tobycm/skibidi-phone-usb-hub/pcb/skibidi-phone-usb-hub.kicad_sch

## KiCad design pcb/skibidi-phone-usb-hub.kicad_sch (2026-04-20)

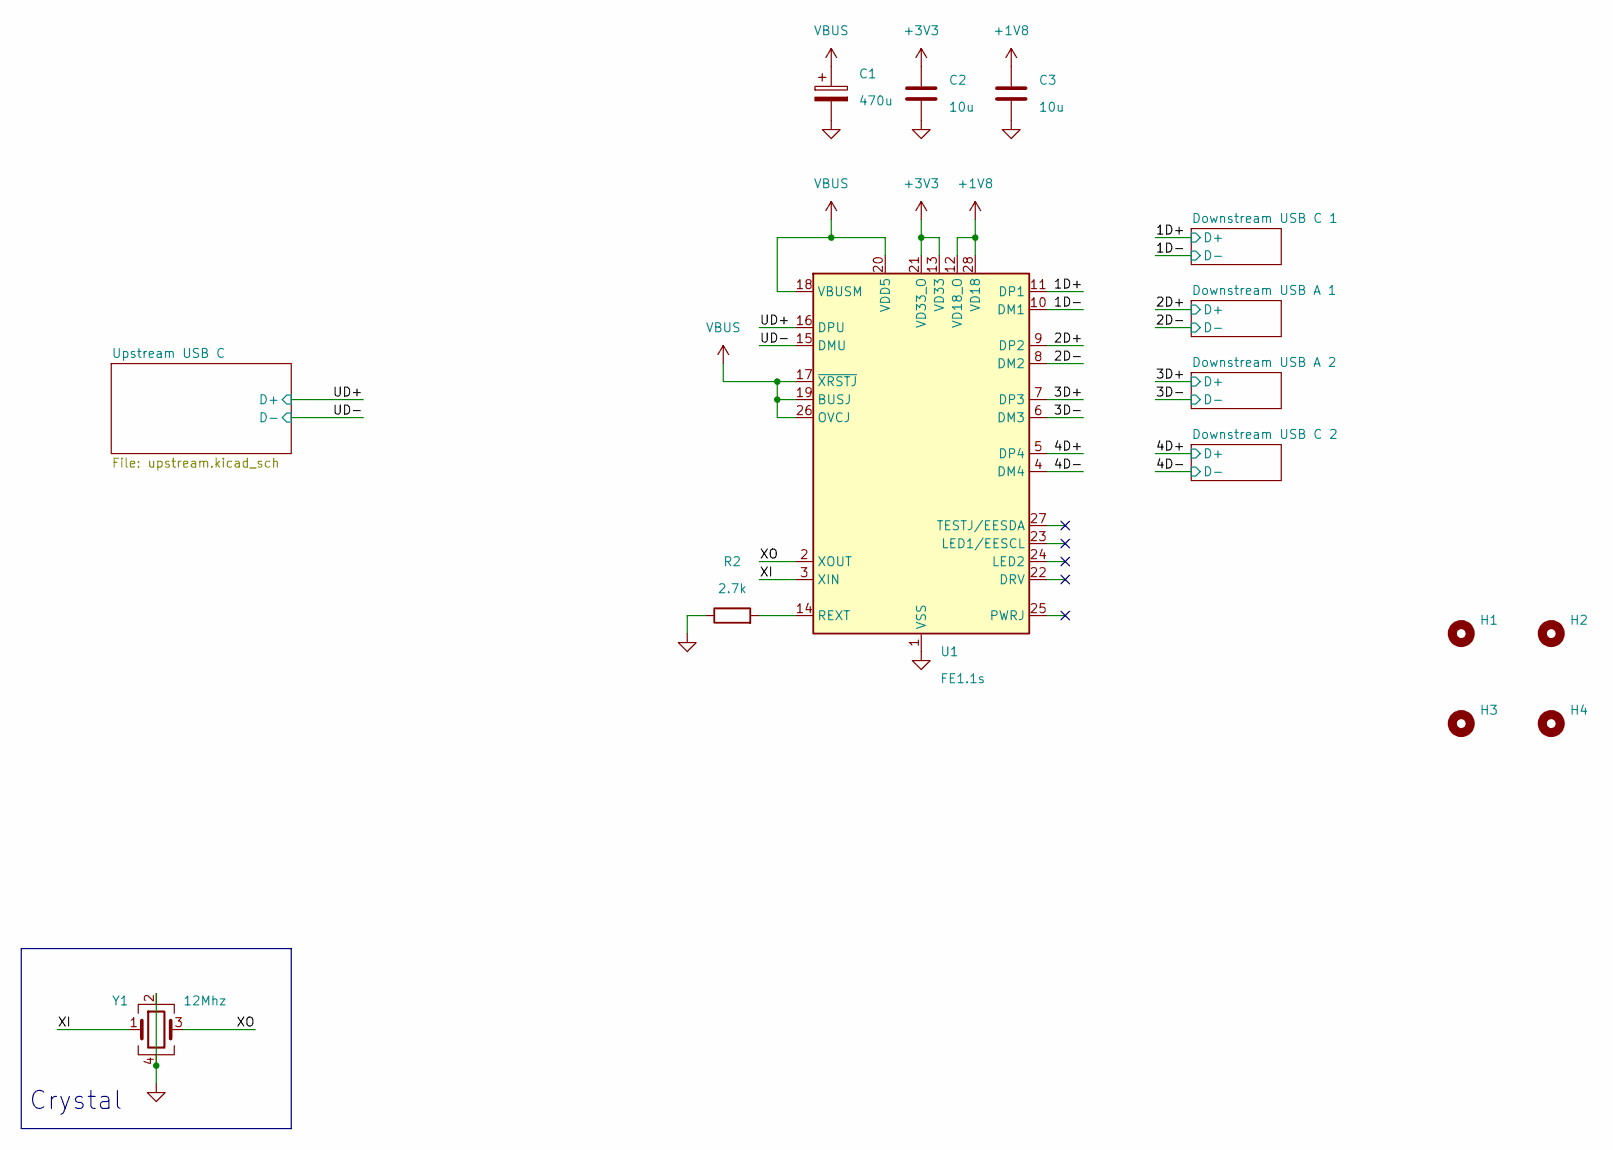
[picture p19: schematic skibidi-phone-usb-hub.kicad_sch]

Parts:
C1: 470u; CP_Radial_D8.0mm_P3.50mm; LCSC Part C49232874
C2, C3: 10u; C_0603_1608Metric; LCSC Part C96446
H1, H2, H3, H4: MountingHole; MountingHole_3.2mm_M3_Pad
R2: 2.7k; R_0603_1608Metric; LCSC Part C2907008
U1: FE1.1s; SSOP-28_3.9x9.9mm_P0.635mm; LCSC Part C9359
Y1: 12Mhz; Crystal_SMD_3225-4Pin_3.2x2.5mm; LCSC Part C5280578

Connections:
1D+: U1.11 (DP1)
1D-: U1.10 (DM1)
2D+: U1.9 (DP2)
2D-: U1.8 (DM2)
3D+: U1.7 (DP3)
3D-: U1.6 (DM3)
4D+: U1.5 (DP4)
4D-: U1.4 (DM4)
+1V8: C3.1, U1.12 (VD18_O), U1.28 (VD18)
+3V3: C2.1, U1.13 (VD33), U1.21 (VD33_O)
GND: C1.2, C2.2, C3.2, R2.1, U1.1 (VSS), Y1.2, Y1.4
unnamed: R2.2, U1.14 (REXT)
UD+: U1.16 (DPU)
UD-: U1.15 (DMU)
VBUS: C1.1, U1.17 (~XRSTJ), U1.18 (VBUSM), U1.19 (BUSJ), U1.20 (VDD5), U1.26 (OVCJ)
XI: U1.3 (XIN), Y1.1
XO: U1.2 (XOUT), Y1.3

Notes on the sheet:
Crystal
