tobycm/skibidi-phone-usb-hub/pcb/upstream.kicad_sch

## KiCad design pcb/upstream.kicad_sch (2026-04-20)

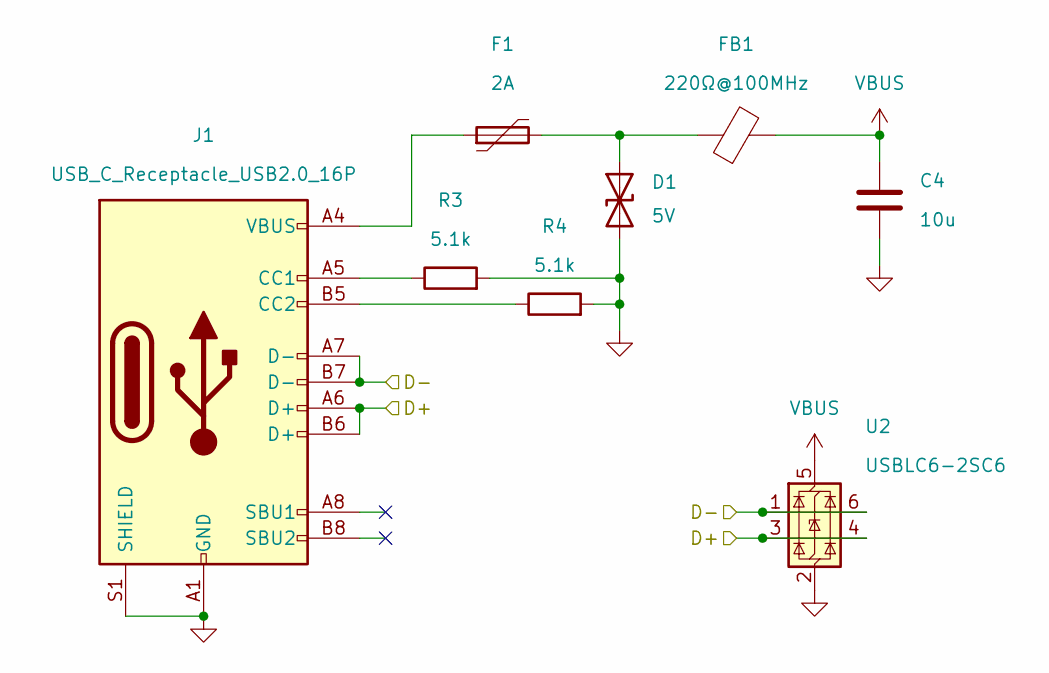
[picture p20: schematic upstream.kicad_sch]

Parts:
C4: 10u; C_0603_1608Metric; LCSC Part C96446
D1: 5V; D_SOD-523; LCSC Part C82044
F1: 2A; Fuse_1206_3216Metric; LCSC Part C883135
FB1: 220Ω@100MHz; R_0805_2012Metric_Pad1.20x1.40mm_HandSolder; LCSC Part C85840
J1: USB_C_Receptacle_USB2.0_16P; USB-C-SMD_TYPE-C-6PIN-2MD-073; LCSC Part C2765186
R3, R4: 5.1k; R_0603_1608Metric; LCSC Part C2907044
U2: USBLC6-2SC6; SOT-23-6; LCSC Part C2827654

Connections:
D+: J1.A6 (D+), J1.B6 (D+), U2.3 (I/O2), U2.4 (I/O2)
D-: J1.A7 (D-), J1.B7 (D-), U2.1 (I/O1), U2.6 (I/O1)
GND: C4.2, D1.2 (A2), J1.A1 (GND), J1.A12 (GND), J1.B1 (GND), J1.B12 (GND), J1.S1 (SHIELD), R3.2, R4.2, U2.2 (GND)
unnamed: D1.1 (A1), F1.2, FB1.1
unnamed: F1.1, J1.A4 (VBUS), J1.A9 (VBUS), J1.B4 (VBUS), J1.B9 (VBUS)
unnamed: J1.A5 (CC1), R3.1
unnamed: J1.B5 (CC2), R4.1
VBUS: C4.1, FB1.2, U2.5 (VBUS)
