tobycm/skibidi-phone-usb-hub/pcb/usb_a.kicad_sch

## KiCad design pcb/usb_a.kicad_sch (2026-04-20)

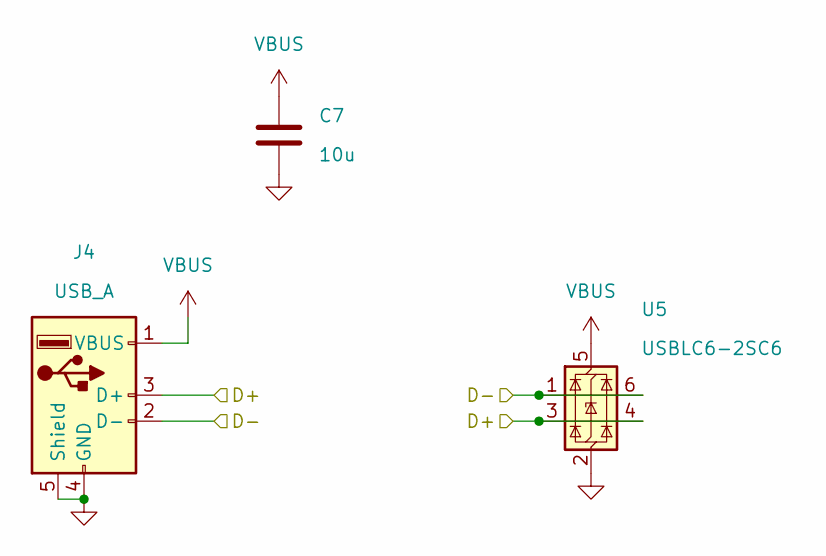
[picture p21: schematic usb_a.kicad_sch]

Parts:
C7: 10u; C_0603_1608Metric; LCSC Part C96446
J4: USB_A; USB-A-TH_AF-WJDG; LCSC Part C456018
U5: USBLC6-2SC6; SOT-23-6; LCSC Part C2827654

Connections:
D+: J4.3 (D+), U5.3 (I/O2), U5.4 (I/O2)
D-: J4.2 (D-), U5.1 (I/O1), U5.6 (I/O1)
GND: C7.2, J4.4 (GND), J4.5 (Shield), U5.2 (GND)
VBUS: C7.1, J4.1 (VBUS), U5.5 (VBUS)
