tobycm/skibidi-phone-usb-hub/pcb/usb_c.kicad_sch

## KiCad design pcb/usb_c.kicad_sch (2026-04-20)

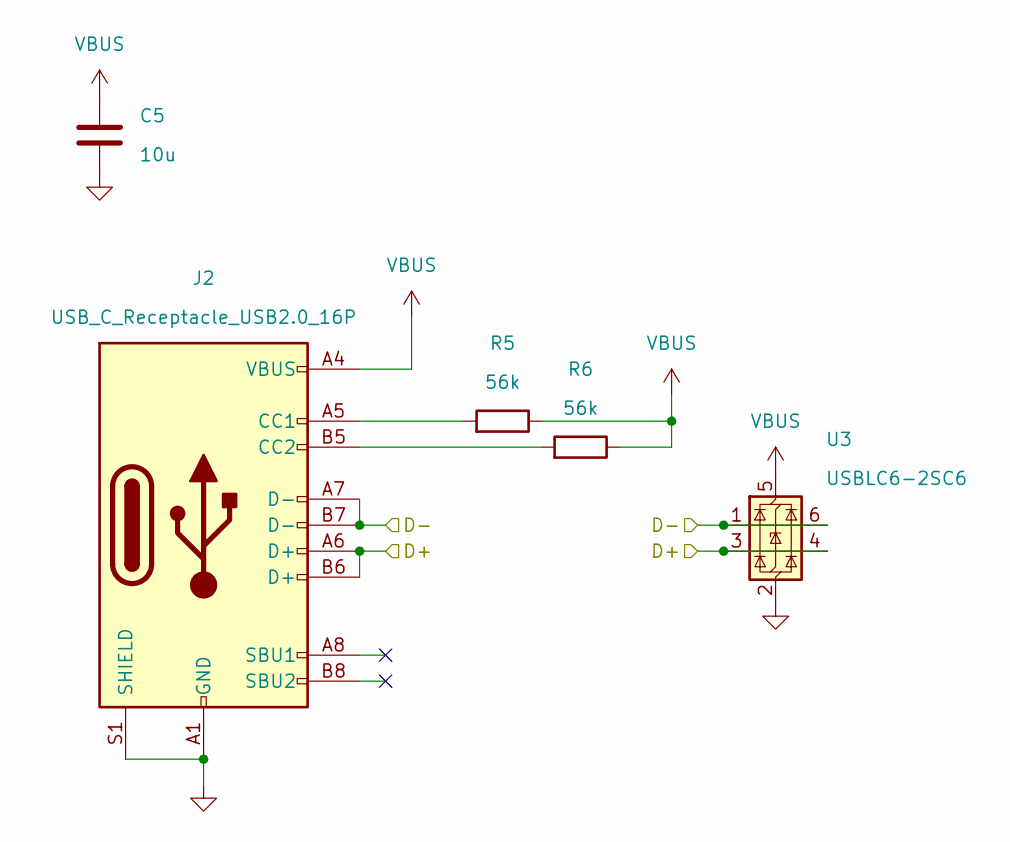
[picture p22: schematic usb_c.kicad_sch]

Parts:
C5: 10u; C_0603_1608Metric; LCSC Part C96446
J2: USB_C_Receptacle_USB2.0_16P; USB-C-SMD_TYPE-C-6PIN-2MD-073; LCSC Part C2765186
R5, R6: 56k; R_0603_1608Metric; LCSC Part C23206
U3: USBLC6-2SC6; SOT-23-6; LCSC Part C2827654

Connections:
D+: J2.A6 (D+), J2.B6 (D+), U3.3 (I/O2), U3.4 (I/O2)
D-: J2.A7 (D-), J2.B7 (D-), U3.1 (I/O1), U3.6 (I/O1)
GND: C5.2, J2.A1 (GND), J2.A12 (GND), J2.B1 (GND), J2.B12 (GND), J2.S1 (SHIELD), U3.2 (GND)
unnamed: J2.A5 (CC1), R5.2
unnamed: J2.B5 (CC2), R6.2
VBUS: C5.1, J2.A4 (VBUS), J2.A9 (VBUS), J2.B4 (VBUS), J2.B9 (VBUS), R5.1, R6.1, U3.5 (VBUS)
